Ezkabalari/TallerDomotica22_23/imagenes/1 -1.jpg

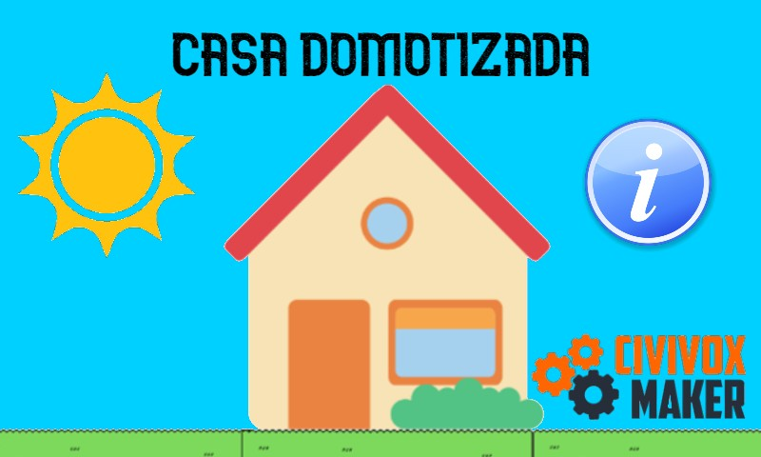
imagenes/1 -1.jpg
