Ezkabalari/TallerDomotica22_23/imagenes/2.jpg

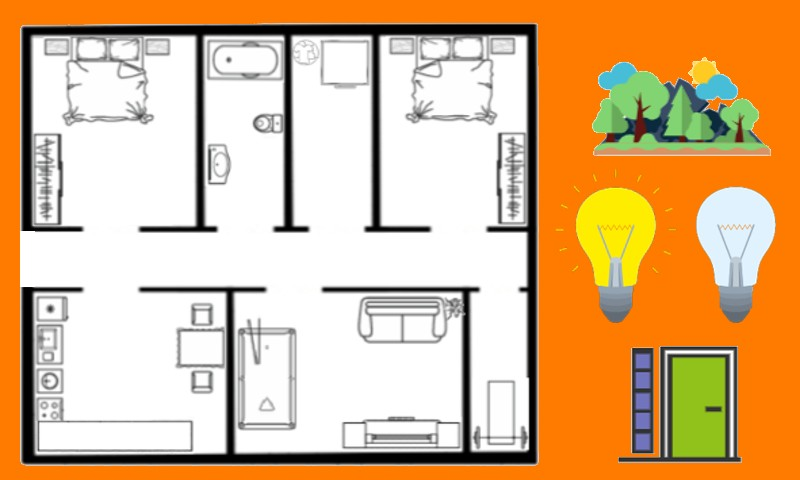
imagenes/2.jpg
