Ezkabalari/TallerDomotica22_23/imagenes/3 - 1.jpg

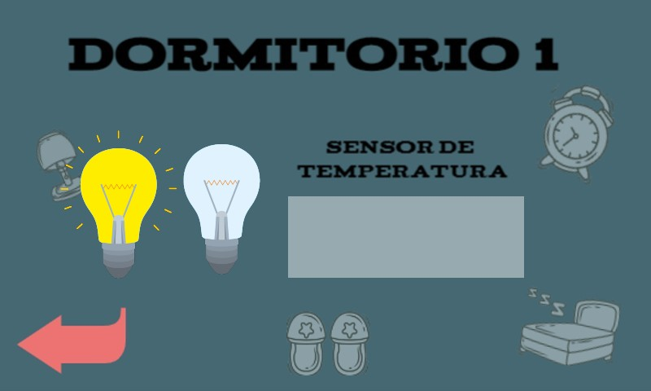
imagenes/3 - 1.jpg
