Ezkabalari/TallerDomotica22_23/imagenes/3 - 2.jpg

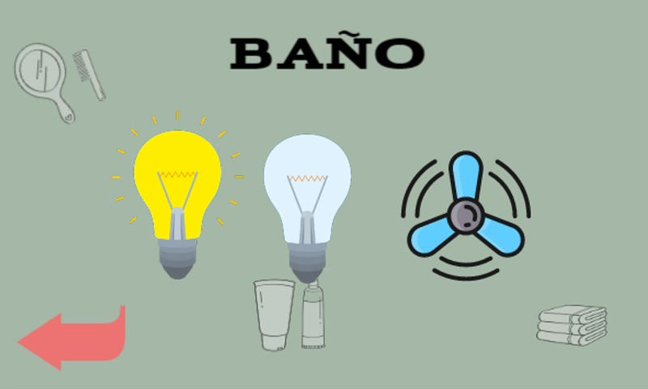
imagenes/3 - 2.jpg
