Ezkabalari/TallerDomotica22_23/imagenes/3 - 3.jpg

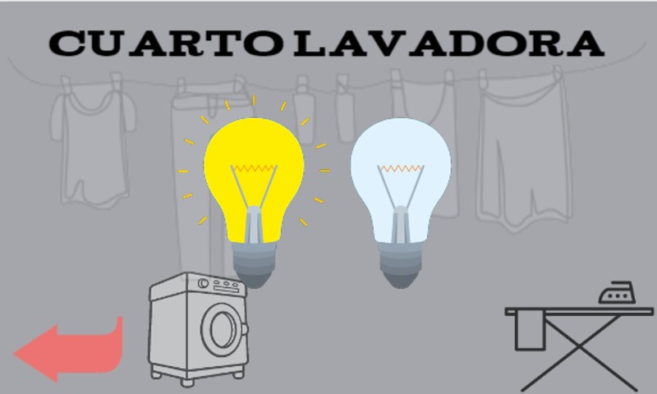
imagenes/3 - 3.jpg
