Ezkabalari/TallerDomotica22_23/imagenes/3 - 4.jpg

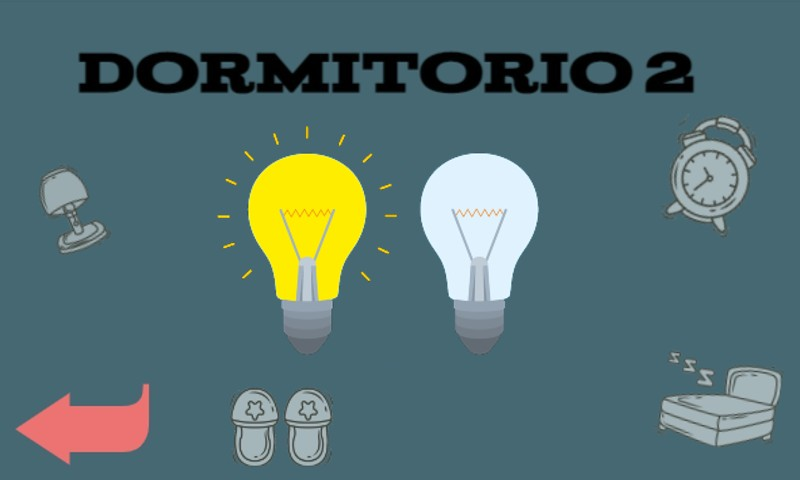
imagenes/3 - 4.jpg
