Ezkabalari/TallerDomotica22_23/imagenes/3 - 5.jpg

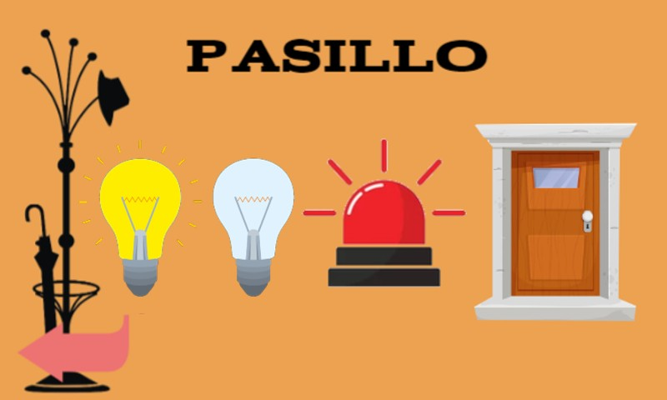
imagenes/3 - 5.jpg
