Ezkabalari/TallerDomotica22_23/imagenes/3 - 6.jpg

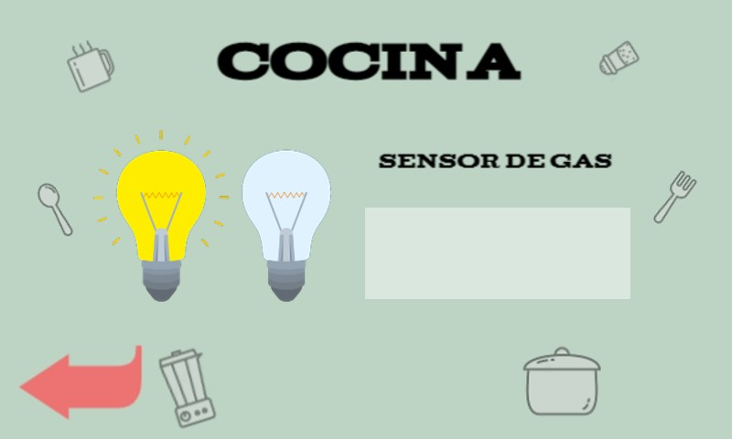
imagenes/3 - 6.jpg
