Ezkabalari/TallerDomotica22_23/imagenes/3 - 7.jpg

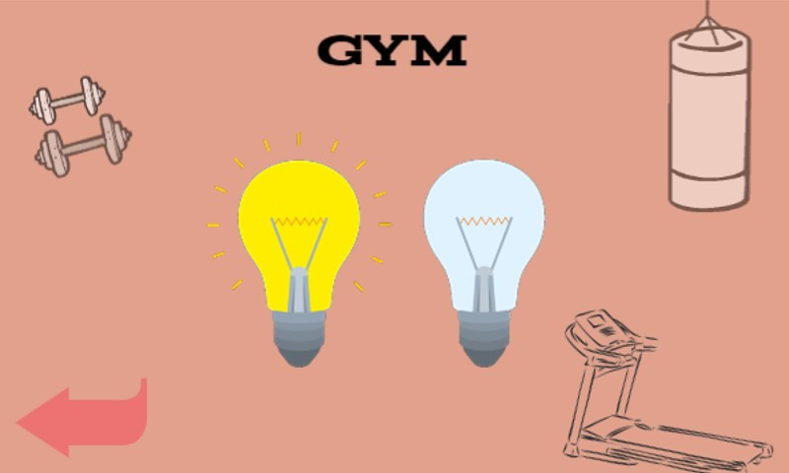
imagenes/3 - 7.jpg
