Ezkabalari/TallerDomotica22_23/Modelos 3d/Muebles/img_2533.png

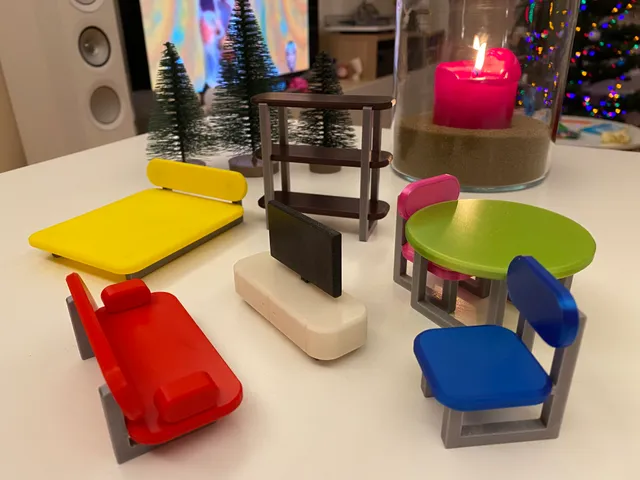
Modelos 3d/Muebles/img_2533.png
