Ezkabalari/TallerDomotica22_23/Modelos 3d/Muebles/Armario/Armario.stl

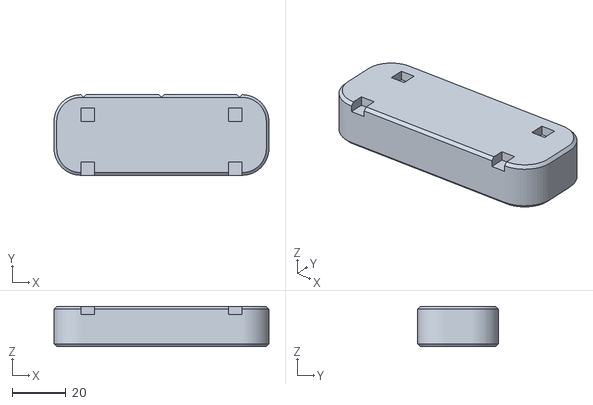
[picture p30: CAD file, 2023-01-23]
Modelos 3d/Muebles/Armario/Armario.stl
80.0 x 30.0 x 15.0
