Ezkabalari/TallerDomotica22_23/Modelos 3d/Muebles/Cama/Cama-Pata x2.stl

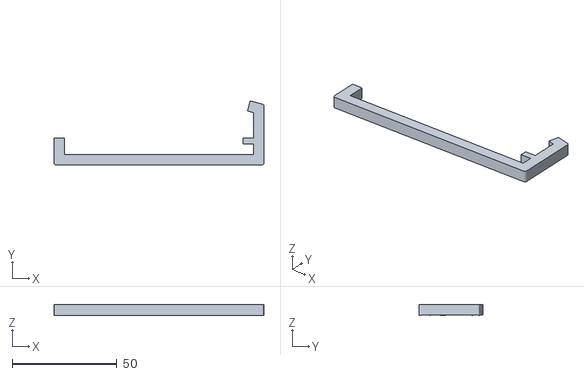
[picture p31: CAD file, 2023-01-23]
Modelos 3d/Muebles/Cama/Cama-Pata x2.stl
100.0 x 30.6 x 5.00
