Ezkabalari/TallerDomotica22_23/Modelos 3d/Muebles/Silla/Silla-Respaldo.stl

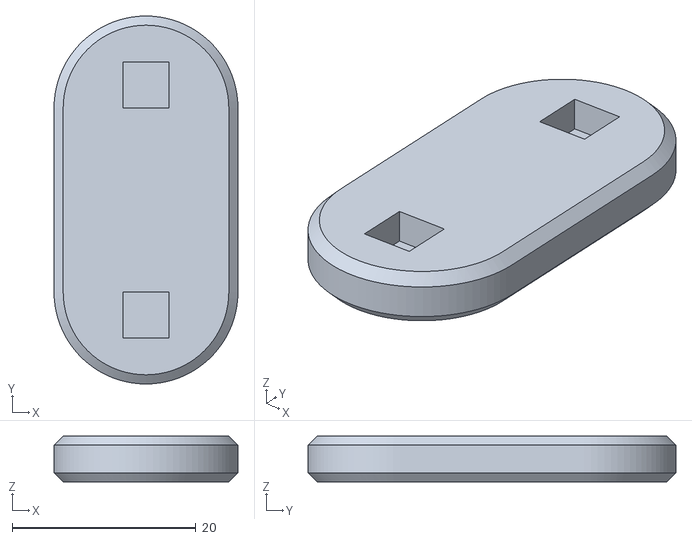
[picture p32: CAD file, 2023-01-23]
Modelos 3d/Muebles/Silla/Silla-Respaldo.stl
20.0 x 40.0 x 5.00
