Ezkabalari/TallerDomotica22_23/Modelos 3d/Muebles/Sofa/Sofa-Pata x2.stl

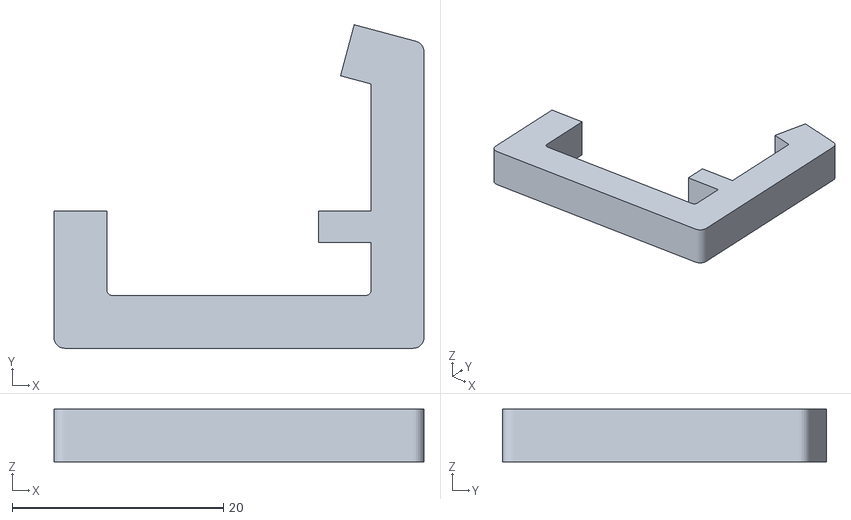
[picture p33: CAD file, 2023-01-23]
Modelos 3d/Muebles/Sofa/Sofa-Pata x2.stl
35.0 x 30.6 x 5.00
