Ezkabalari/TallerDomotica22_23/Modelos 3d/Casa/Casa completa.stl

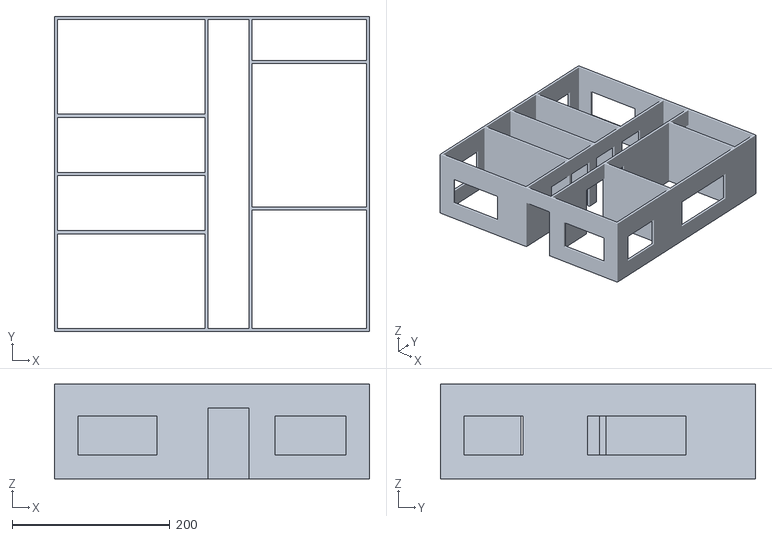
[picture p34: CAD file, 2023-01-23]
Modelos 3d/Casa/Casa completa.stl
400.0 x 400.0 x 120.0
