Ezkabalari/TallerDomotica22_23/Modelos 3d/Muebles/Sofa/Sofa-Almohada x2.stl

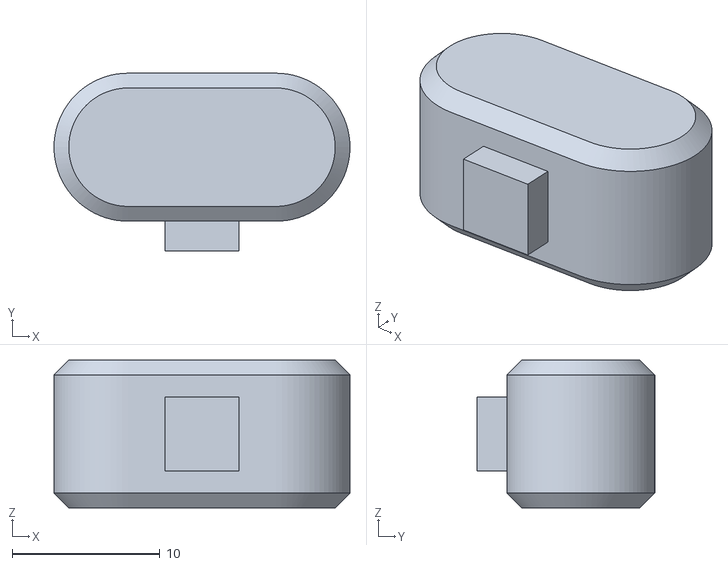
[picture p35: CAD file, 2023-01-23]
Modelos 3d/Muebles/Sofa/Sofa-Almohada x2.stl
20.0 x 12.0 x 10.0
