Ezkabalari/TallerDomotica22_23/Modelos 3d/Casa/Parte 2.stl

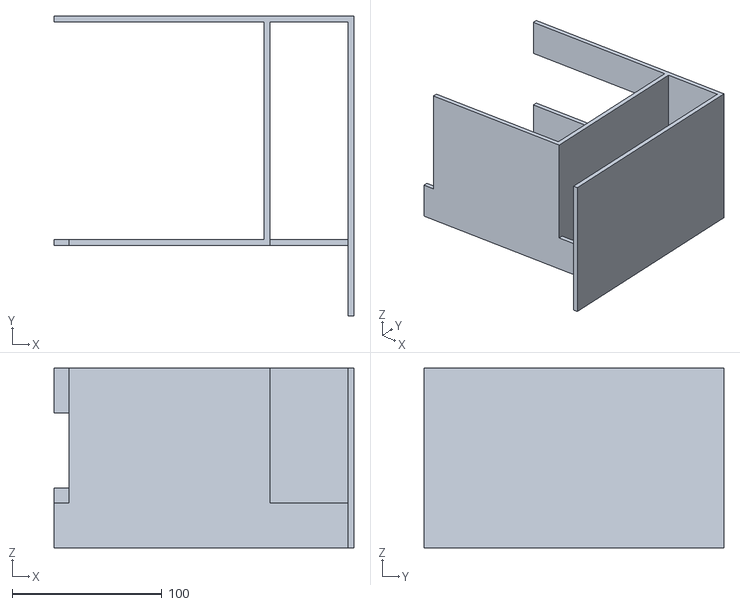
[picture p36: CAD file, 2023-01-23]
Modelos 3d/Casa/Parte 2.stl
200.0 x 200.0 x 120.0
